Temple-of-Epiphany/fan_controllers/output_orca_3mf/SmartSolar_MPPT_250-60-Tr_40mm.3mf

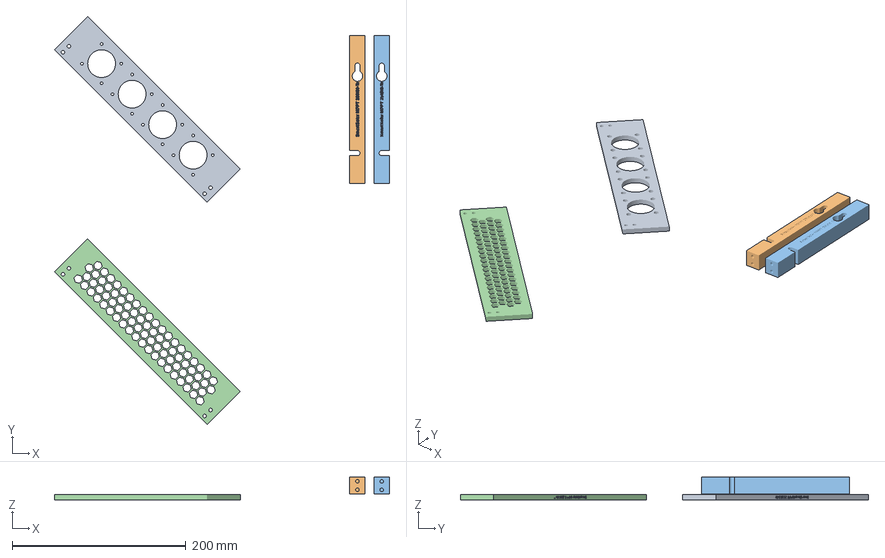
[picture p15: CAD file, 2026-02-24]
output_orca_3mf/SmartSolar_MPPT_250-60-Tr_40mm.3mf
386.0 x 470.0 x 26.2 mm
Front Fan Mount
Left Rail
Right Rail
Rear Grill
