Temple-of-Epiphany/fan_controllers/output_orca_3mf/SmartSolar_MPPT_150-35_50mm.3mf

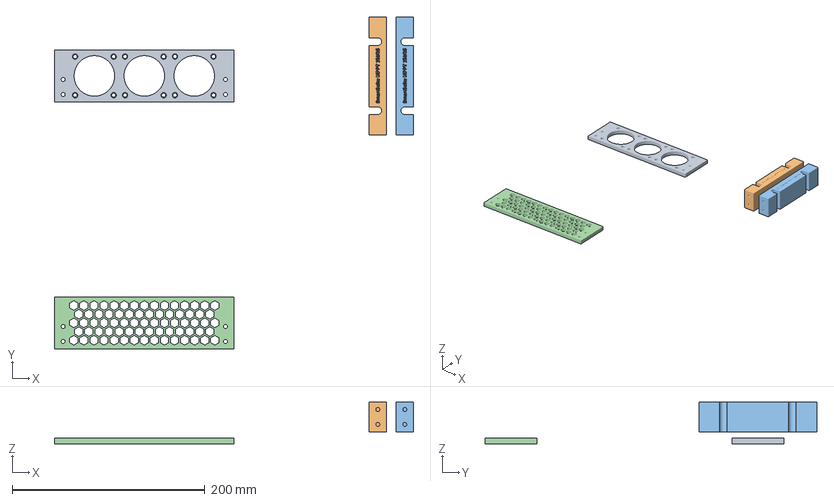
[picture p16: CAD file, 2026-02-24]
output_orca_3mf/SmartSolar_MPPT_150-35_50mm.3mf
372.1 x 344.0 x 43.5 mm
Front Fan Mount
Left Rail
Right Rail
Rear Grill
