Temple-of-Epiphany/fan_controllers/output_orca_3mf/SmartSolar_MPPT_150-70-Tr_VE_Can_50mm.3mf

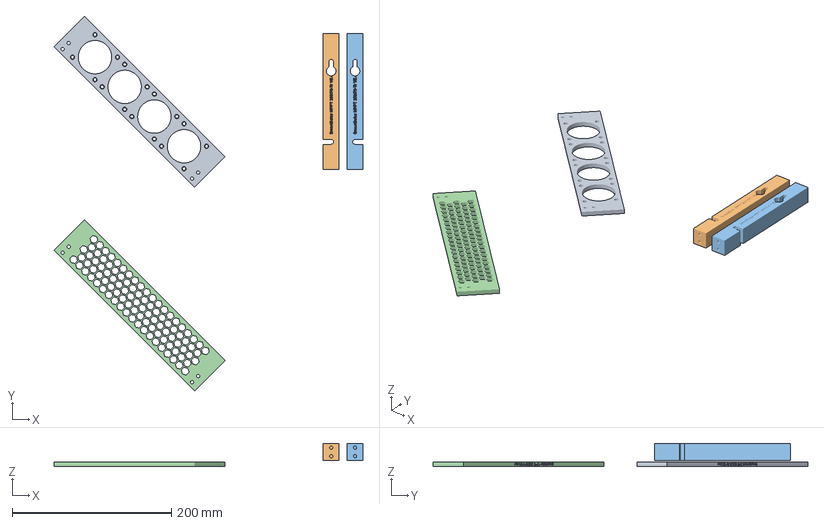
[picture p17: CAD file, 2026-02-24]
output_orca_3mf/SmartSolar_MPPT_150-70-Tr_VE_Can_50mm.3mf
388.6 x 471.1 x 29.2 mm
Front Fan Mount
Left Rail
Right Rail
Rear Grill
