Temple-of-Epiphany/fan_controllers/output_orca_3mf/SmartSolar_MPPT_100-20_40mm.3mf

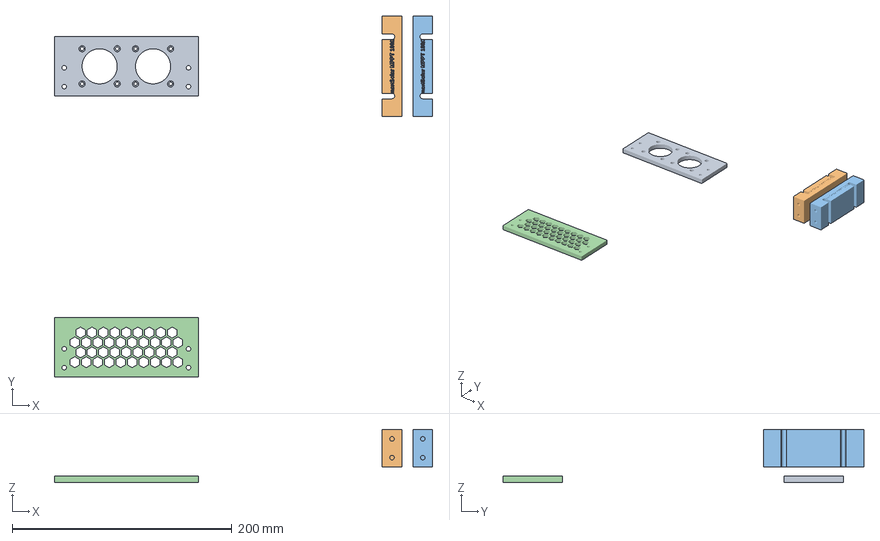
[picture p18: CAD file, 2026-02-24]
output_orca_3mf/SmartSolar_MPPT_100-20_40mm.3mf
344.6 x 328.9 x 48.3 mm
Front Fan Mount
Left Rail
Right Rail
Rear Grill
