Temple-of-Epiphany/fan_controllers/output_orca_3mf/SmartSolar_MPPT_100-15-C2_40mm.3mf

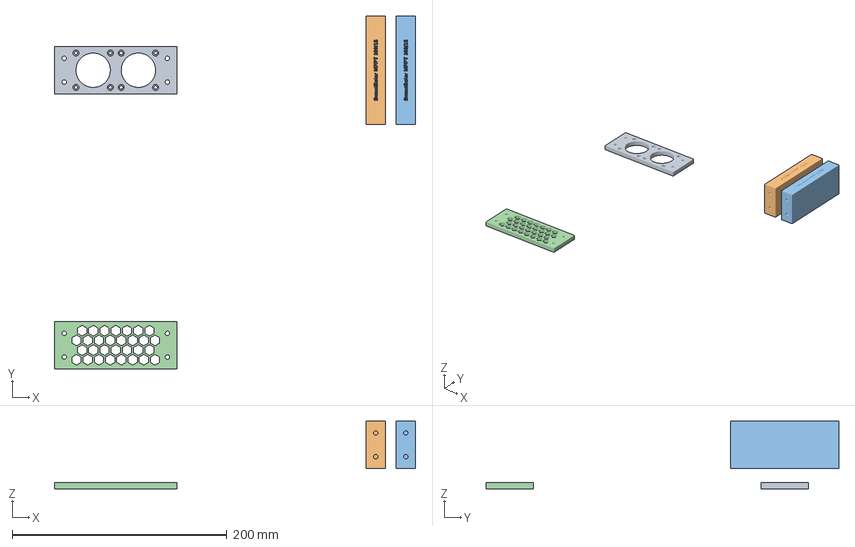
[picture p19: CAD file, 2026-02-24]
output_orca_3mf/SmartSolar_MPPT_100-15-C2_40mm.3mf
336.1 x 328.4 x 63.0 mm
Front Fan Mount
Left Rail
Right Rail
Rear Grill
